touh6/breadplayer/images/back cbd.jpeg

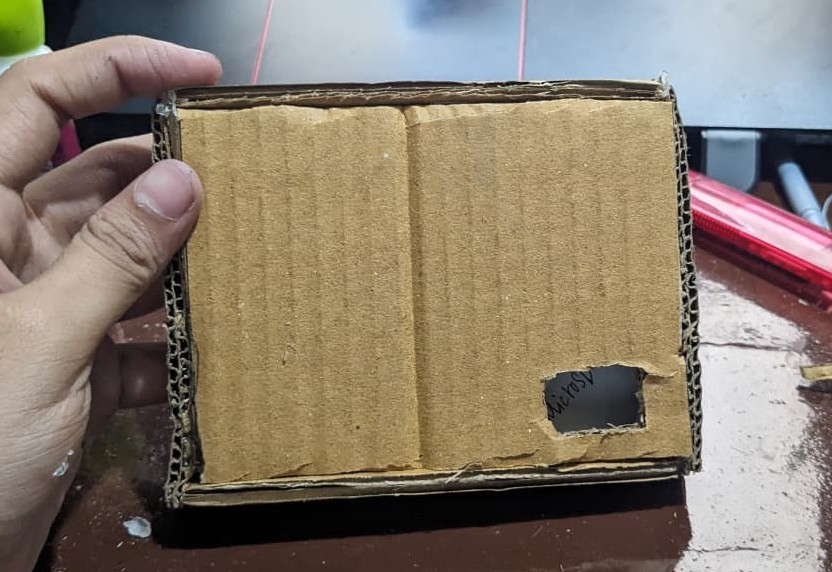
images/back cbd.jpeg
