touh6/breadplayer/images/base cbd.jpeg

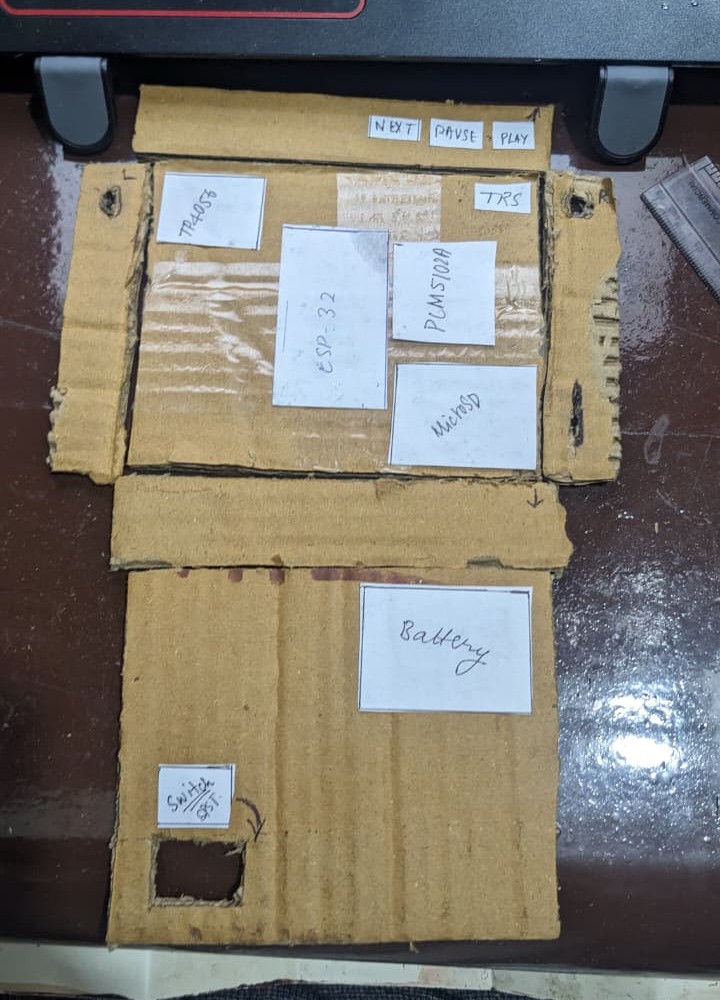
images/base cbd.jpeg
