touh6/breadplayer/images/breadplayer v1.png

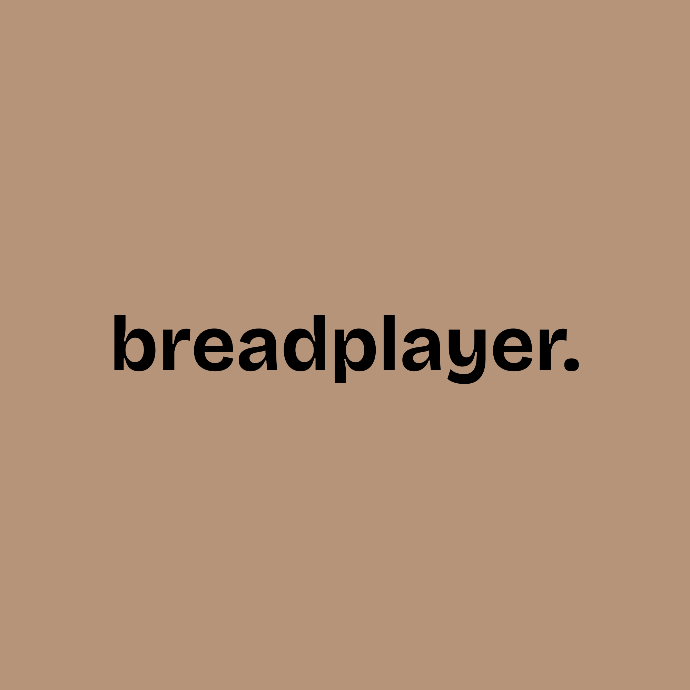
images/breadplayer v1.png
