touh6/breadplayer/images/front cbd.jpeg

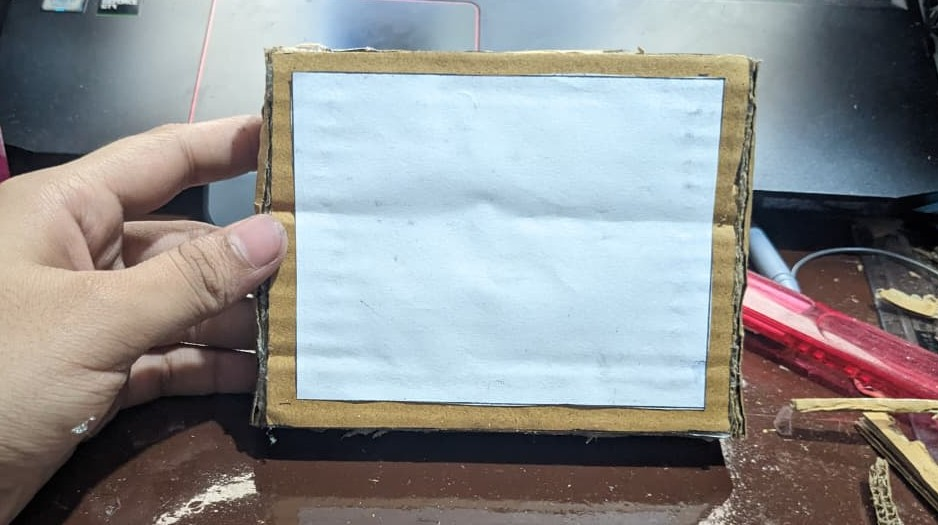
images/front cbd.jpeg
