touh6/breadplayer/images/front.PNG

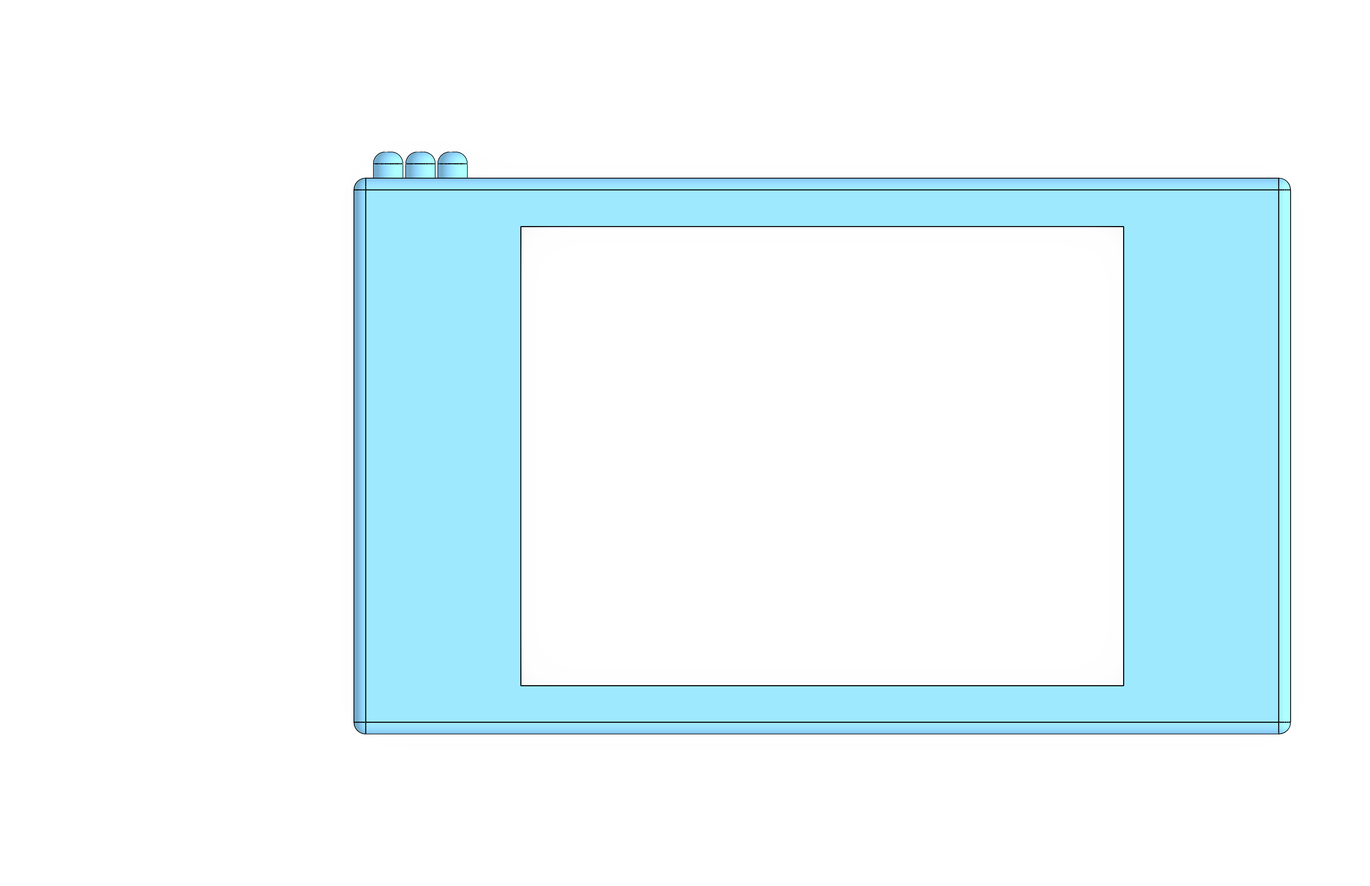
images/front.PNG
