touh6/breadplayer/images/inner guts cbd.jpeg

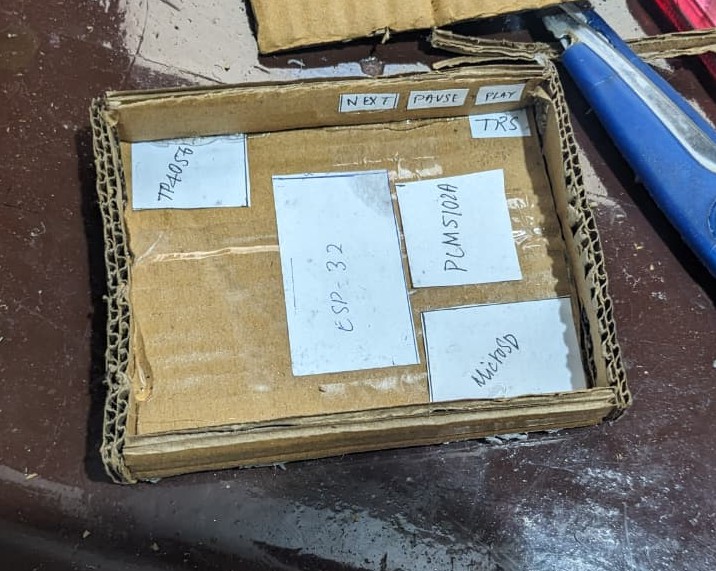
images/inner guts cbd.jpeg
