touh6/breadplayer/images/left-2d.jpg

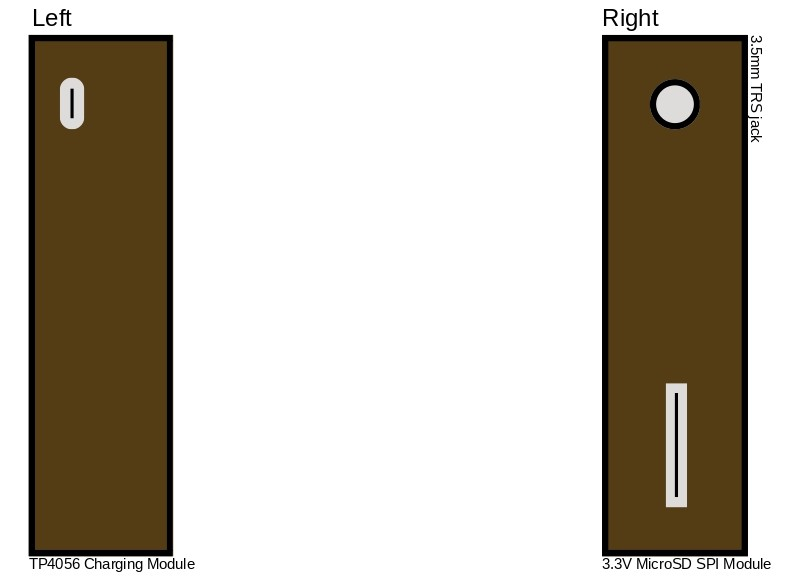
images/left-2d.jpg
