touh6/breadplayer/images/perf board guts.jpeg

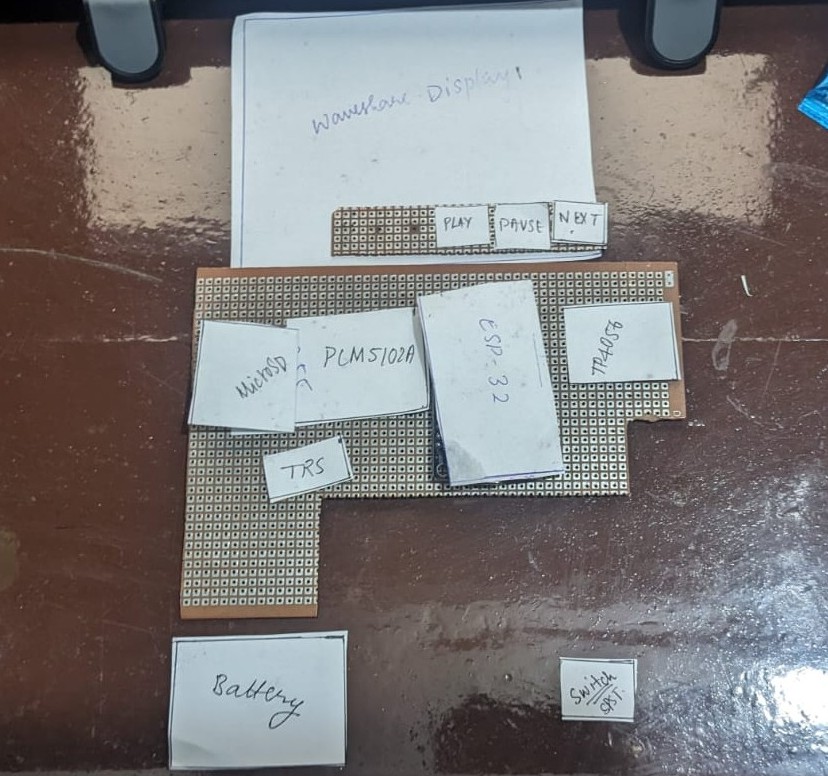
images/perf board guts.jpeg
