touh6/breadplayer/images/perfboard version_bb.png

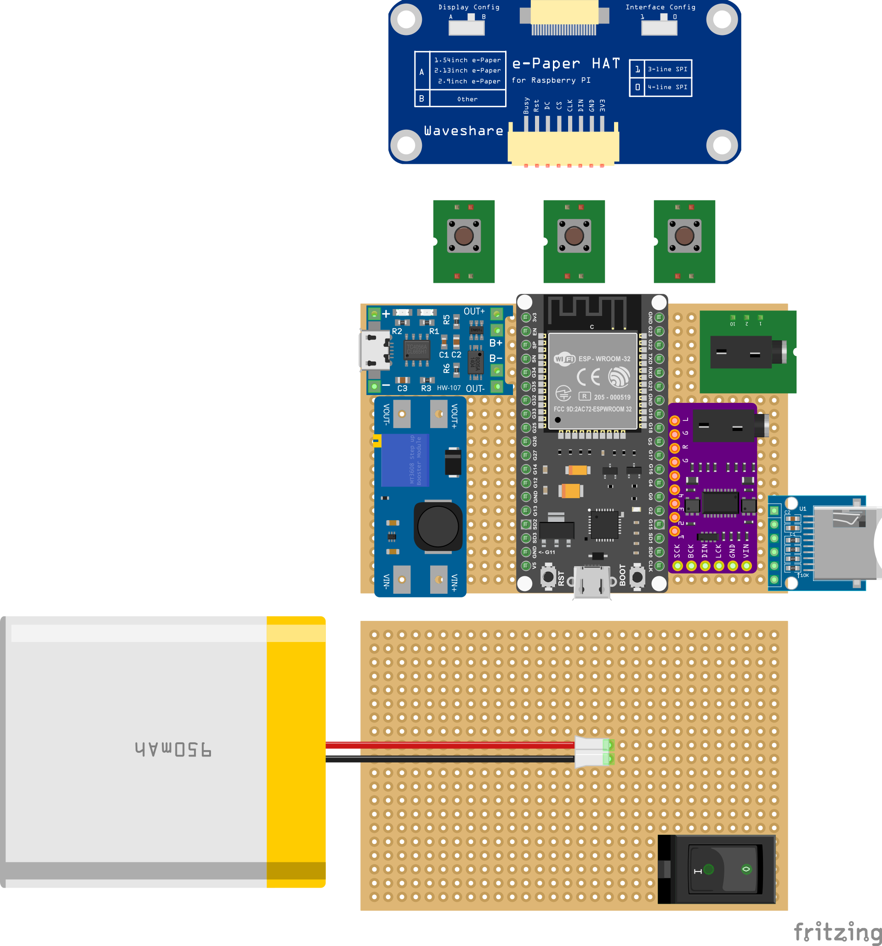
images/perfboard version_bb.png
