touh6/breadplayer/images/right cbd.jpeg

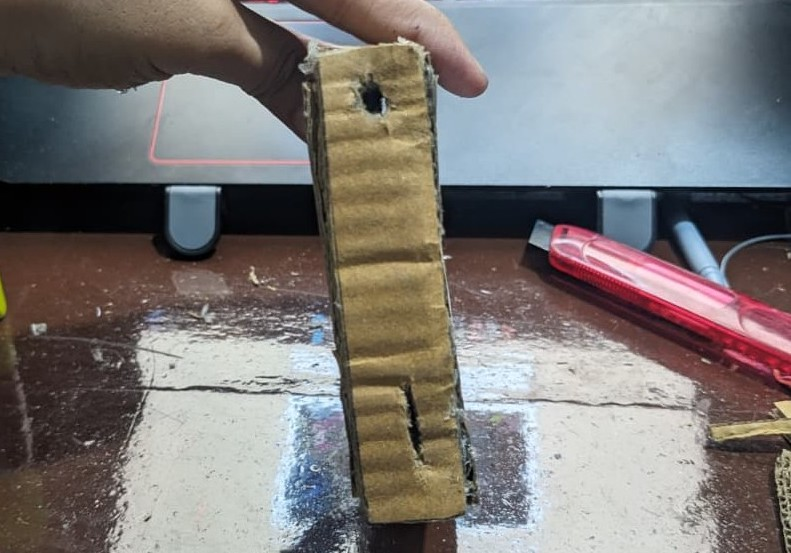
images/right cbd.jpeg
