touh6/breadplayer/images/side.PNG

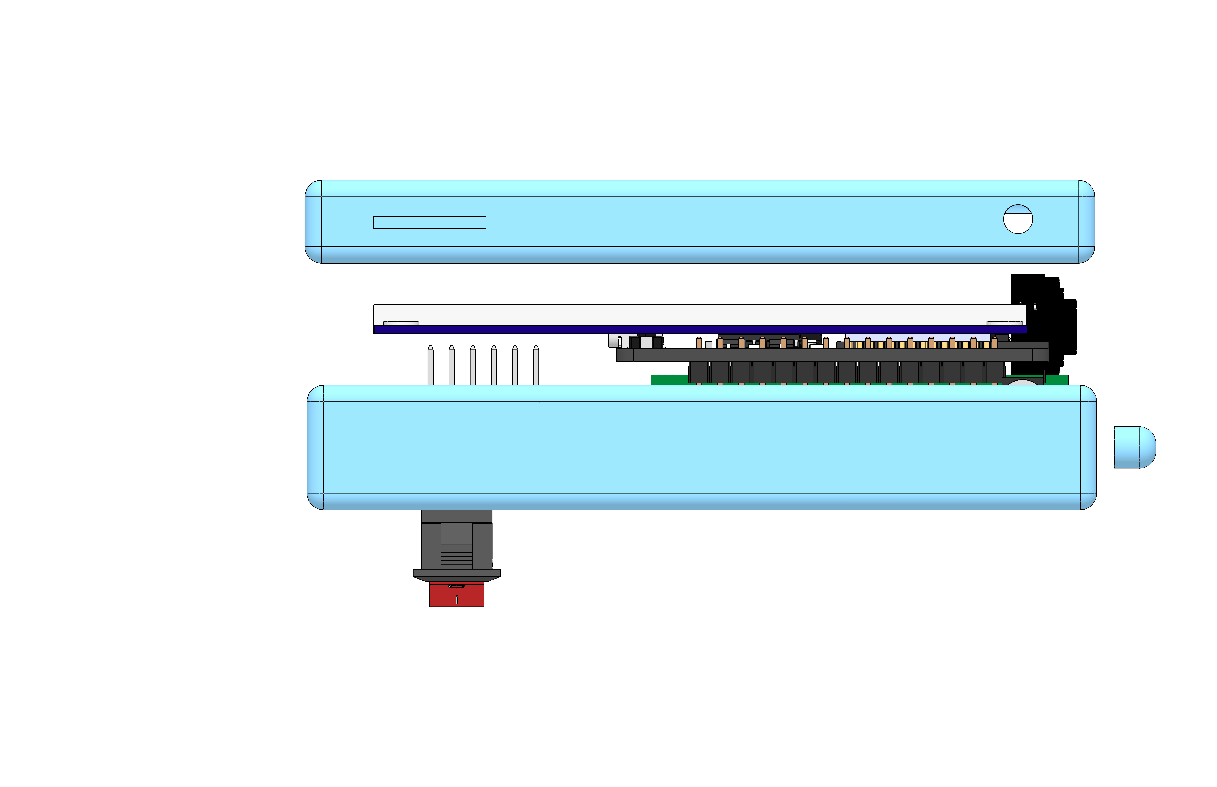
images/side.PNG
