touh6/breadplayer/images/top cbd.jpeg

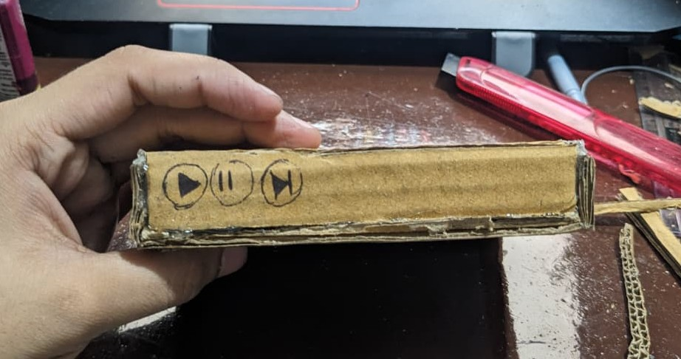
images/top cbd.jpeg
