touh6/breadplayer/images/top.PNG

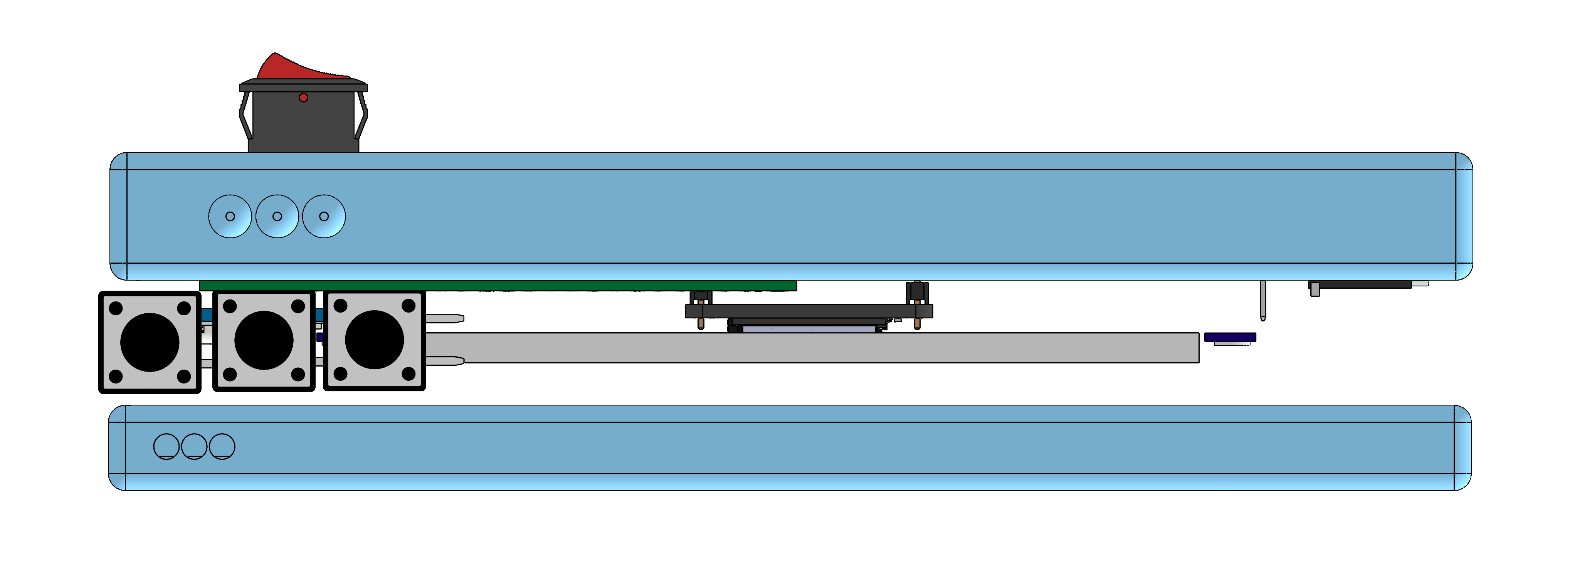
images/top.PNG
