touh6/breadplayer/images/zine.png

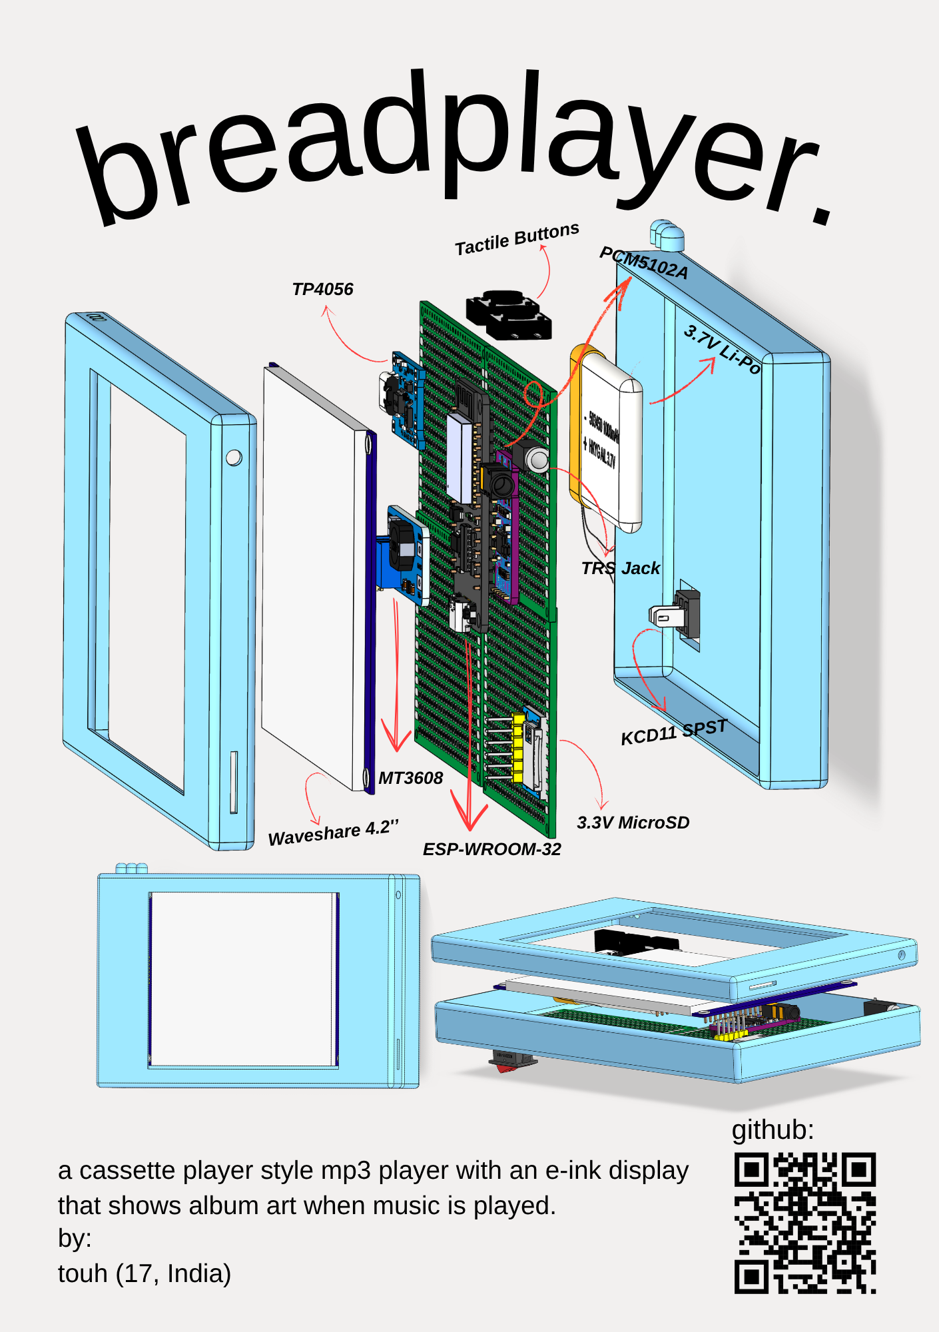
images/zine.png
