touh6/breadplayer/images/assembled.PNG

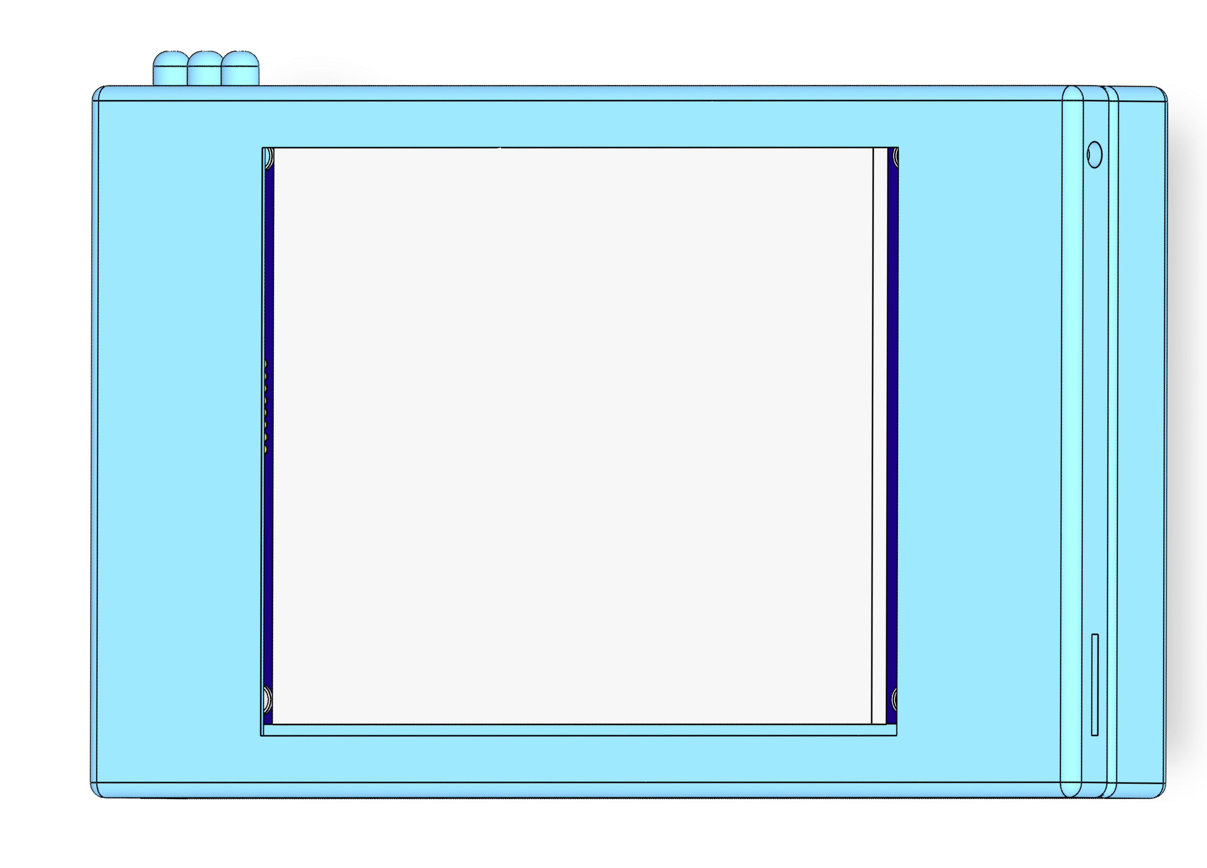
images/assembled.PNG
