touh6/breadplayer/images/assembly btw.PNG

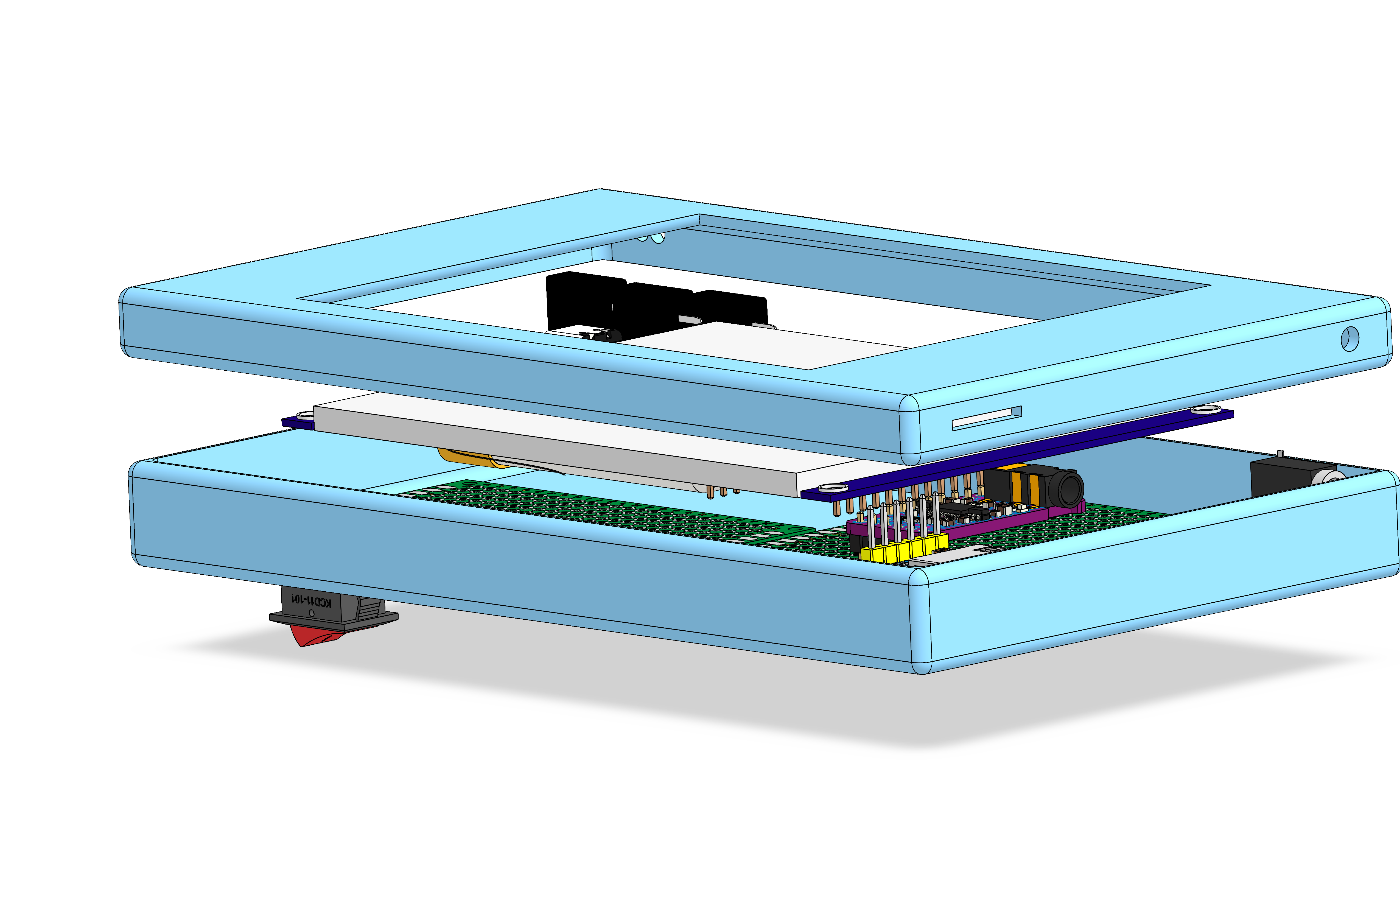
images/assembly btw.PNG
