touh6/breadplayer/images/assembly sdw.PNG

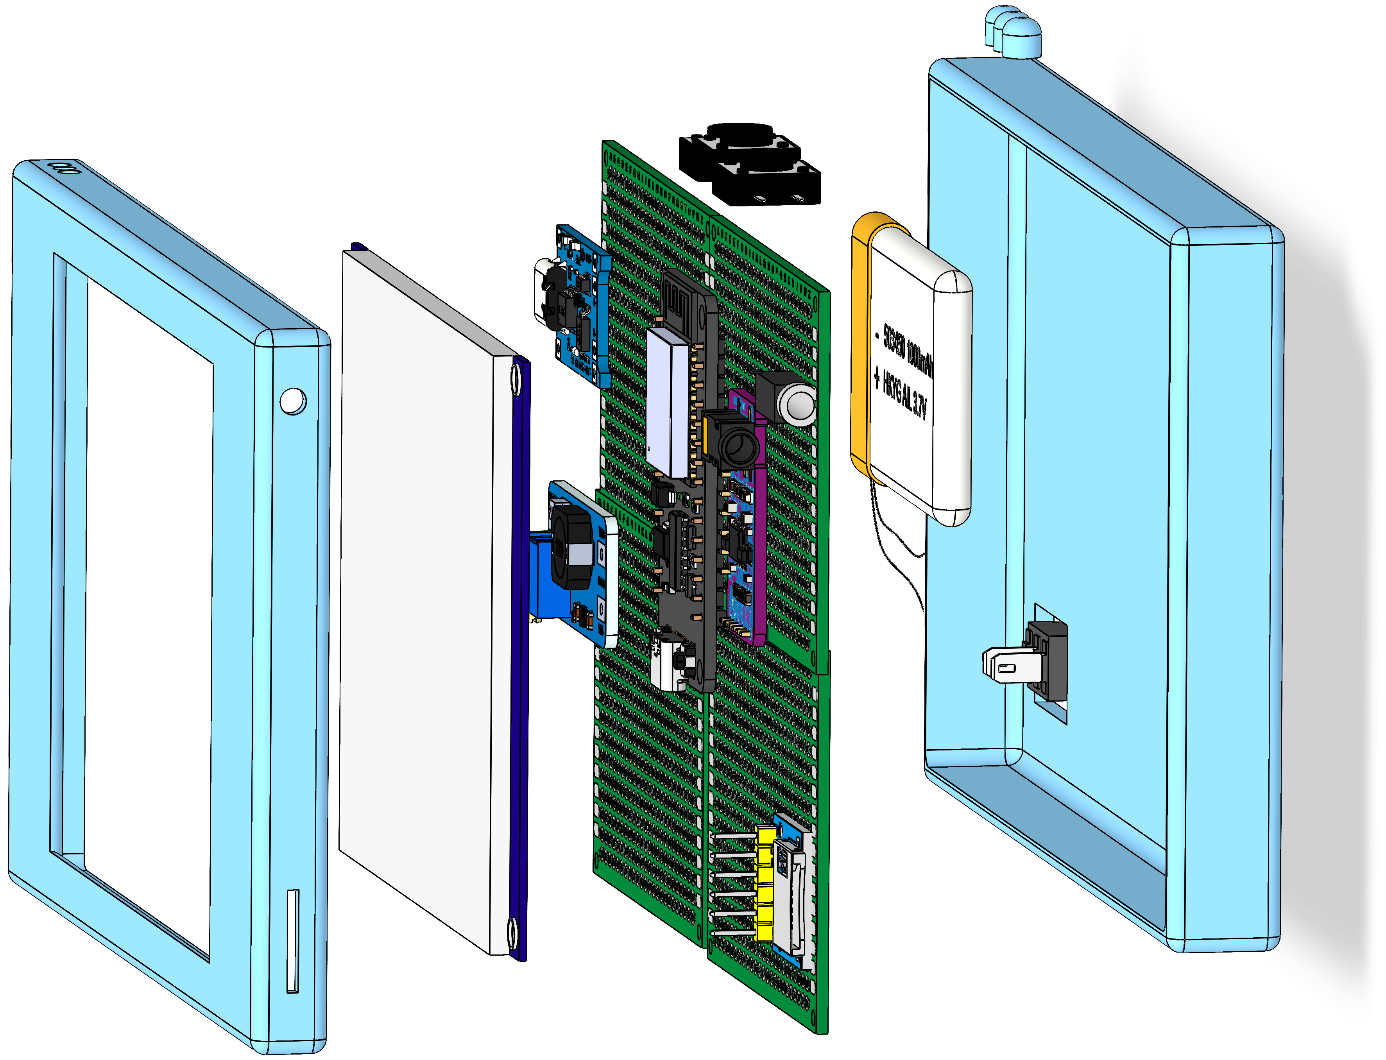
images/assembly sdw.PNG
