touh6/breadplayer/schematic/bpl.kicad_sch

## KiCad design schematic/bpl.kicad_sch (2026-06-16)

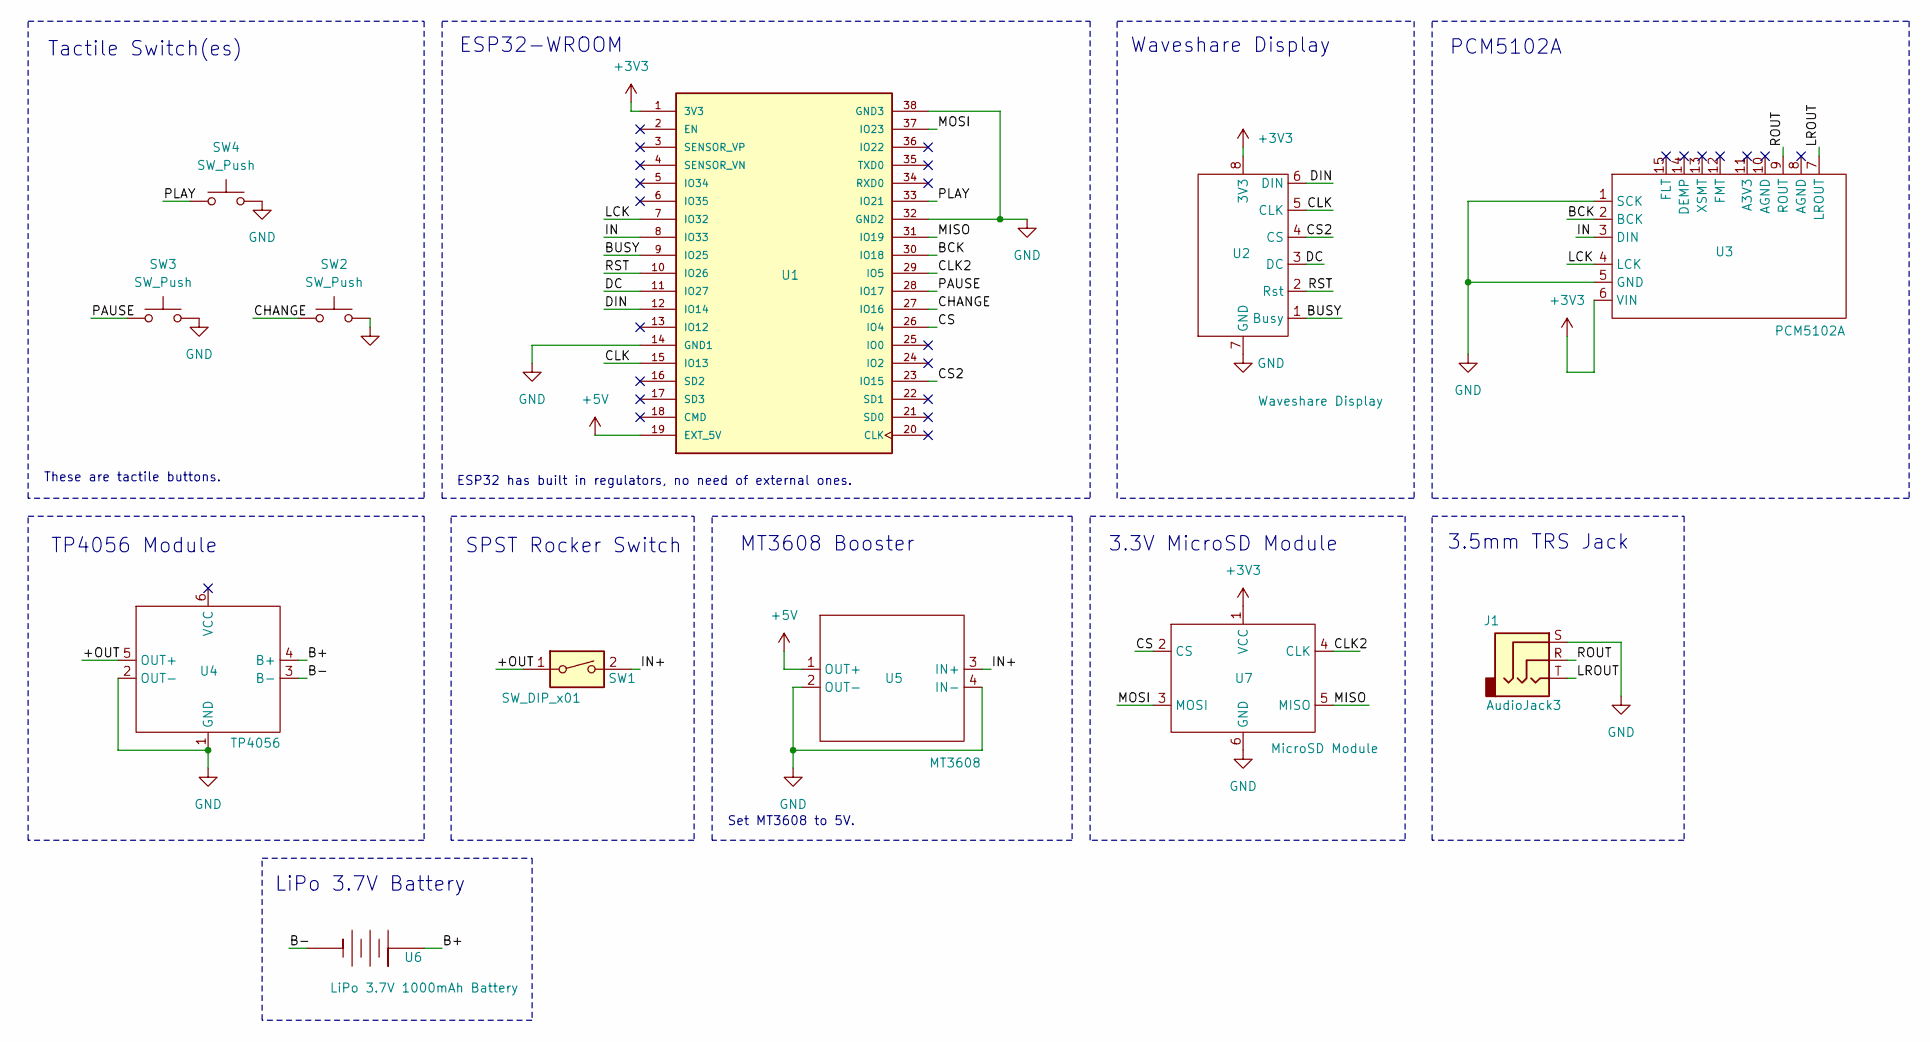
[picture p38: schematic bpl.kicad_sch]

Parts:
J1: AudioJack3
SW1: SW_DIP_x01
SW2, SW3, SW4: SW_Push
U1: DEVKIT_V1_ESP32-WROOM-32; MODULE_DEVKIT_V1_ESP32-WROOM-32; PARTREV N/A
U2: Waveshare Display
U3: PCM5102A
U4: TP4056
U5: MT3608
U6: LiPo 3.7V 1000mAh Battery
U7: MicroSD Module

Connections:
+3V3: U1.1 (3V3), U2.8 (3V3), U3.6 (VIN), U7.1 (VCC)
+5V: U1.19 (EXT_5V), U5.1 (OUT+)
+OUT: SW1.1, U4.5 (OUT+)
B+: U4.4 (B+)
B-: U4.3 (B-)
BCK: U1.30 (IO18), U3.2 (BCK)
BUSY: U1.9 (IO25), U2.1 (Busy)
CHANGE: SW2.1, U1.27 (IO16)
CLK: U1.15 (IO13), U2.5 (CLK)
CLK2: U1.29 (IO5), U7.4 (CLK)
CS: U1.26 (IO4), U7.2 (CS)
CS2: U1.23 (IO15), U2.4 (CS)
DC: U1.11 (IO27), U2.3 (DC)
DIN: U1.12 (IO14), U2.6 (DIN)
GND: J1.S, SW2.2, SW3.2, SW4.2, U1.14 (GND1), U1.32 (GND2), U1.38 (GND3), U2.7 (GND), U3.1 (SCK), U3.5 (GND), U4.1 (GND), U4.2 (OUT-), U5.2 (OUT-), U5.4 (IN-), U7.6 (GND)
IN: U1.8 (IO33), U3.3 (DIN)
IN+: SW1.2, U5.3 (IN+)
LCK: U1.7 (IO32), U3.4 (LCK)
LROUT: J1.T, U3.7 (LROUT)
MISO: U1.31 (IO19), U7.5 (MISO)
MOSI: U1.37 (IO23), U7.3 (MOSI)
PAUSE: SW3.1, U1.28 (IO17)
PLAY: SW4.1, U1.33 (IO21)
ROUT: J1.R, U3.9 (ROUT)
RST: U1.10 (IO26), U2.2 (Rst)

Notes on the sheet:
TP4056 Module
ESP32 has built in regulators, no need of external ones.
These are tactile buttons.
Tactile Switch(es)
MT3608 Booster
3.5mm TRS Jack
PCM5102A
Waveshare Display
ESP32-WROOM
Set MT3608 to 5V.
SPST Rocker Switch
LiPo 3.7V Battery
3.3V MicroSD Module
